MohamedAazir/WirelessEMG/Simulation Files/EMG.asc

+Vs: voltage; +5
C3: cap; 4.7µ
C5: cap; 1µ
C6: cap; 1µ
C7: cap; 0.47µ
C8: cap; 1µ
C9: cap; 0.47µ
C10: cap; 1µ
C11: cap; 0.47µ
C12: cap; 0.47µ
LA1: voltage; ""; AC 1
R1: res; 100k; tol=1
R2: res; 6.8k
R3: res; 100k; tol=1
R5: res; 10k
R6: res; 10k; tol=1
R8: res; 100k
R9: res; 100k
R12: res; 33k
R13: res; 100k
R15: res; 2.2k; tol=1
R21: res; 560
R22: res; 6.8k
R24: res; 470
R25: res; 3.4k
R26: res; 560
R27: res; 470
R30: res; 238k
R31: res; 2k
R: res; 330
R_Var: res; 5k
RA1: voltage; ""; AC 1
U1: AD744
U2: AD744
U3: AD744
U5: AD744
U8: AD744
U9: AD744
U10: AD744
U11: AD744
U12: AD744
V3: voltage; -5
Named nets: 0, +Vs, -Vs, RA, LA
Instrumentational
HPF
LPF
.tran 1s
Power Supply
ECG Signal Acquistion Sim
Notch Filter
.ac dec 100 1 500
